ea4gge/A500Mini-Internal-Functional-Keyboard/A500Mini_Photos/3D_Model_New.jpg

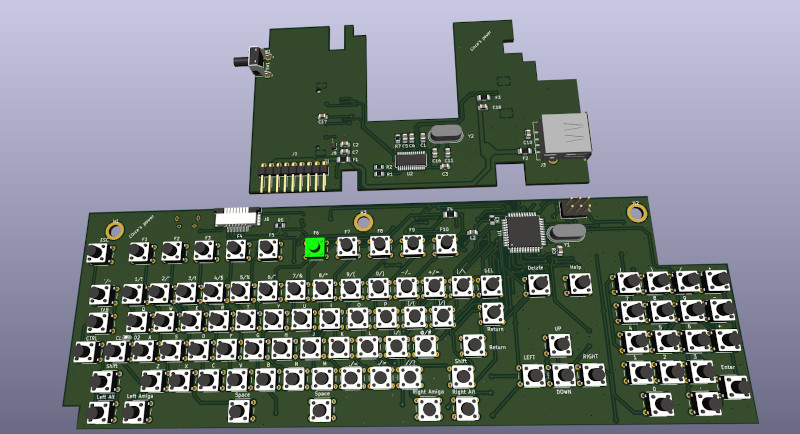
A500Mini_Photos/3D_Model_New.jpg
