ea4gge/A500Mini-Internal-Functional-Keyboard/A500Mini_Photos/0064.jpg

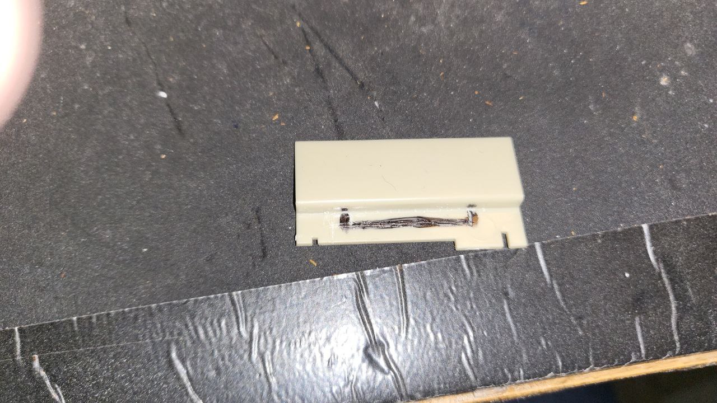
A500Mini_Photos/0064.jpg
