ea4gge/A500Mini-Internal-Functional-Keyboard/A500Mini_Photos/PCB.jpg

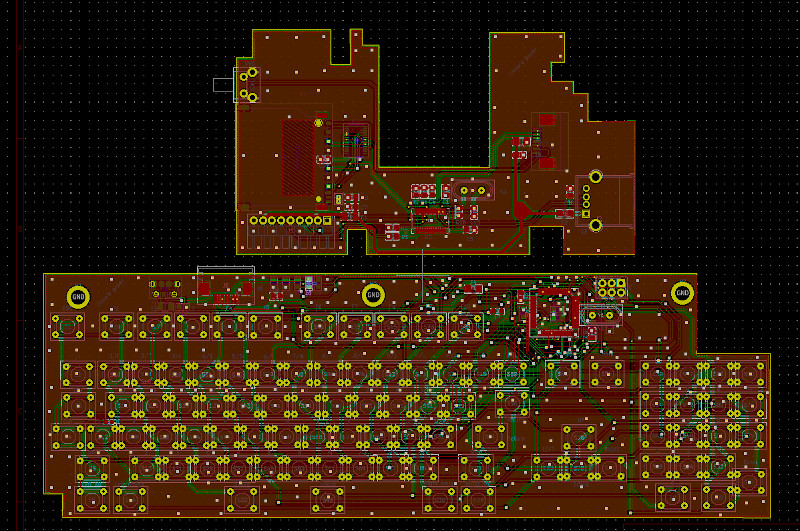
A500Mini_Photos/PCB.jpg
