ea4gge/A500Mini-Internal-Functional-Keyboard/A500Mini_Photos/photo_2022-05-13_19-48-00.jpg

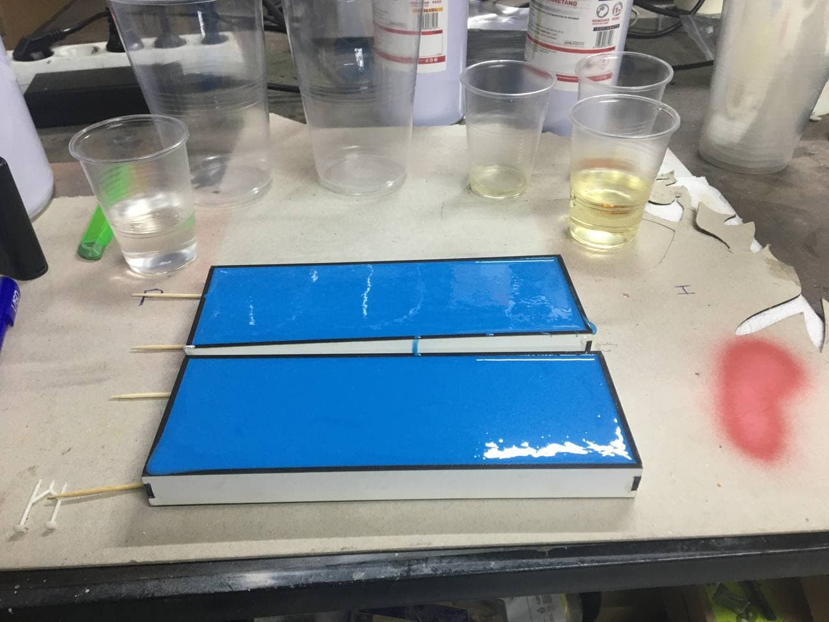
A500Mini_Photos/photo_2022-05-13_19-48-00.jpg
