ea4gge/A500Mini-Internal-Functional-Keyboard/A500Mini_Photos/photo_2022-05-14_19-20-18.jpg

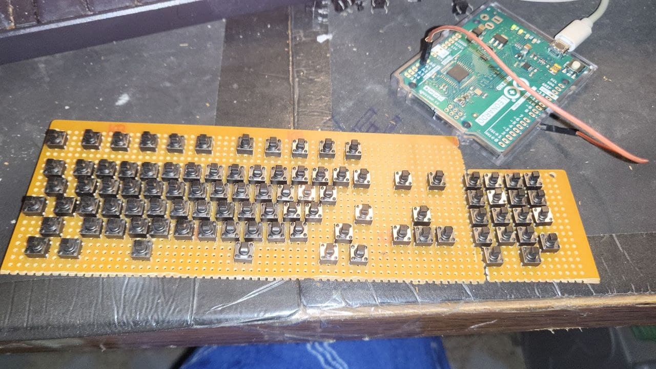
A500Mini_Photos/photo_2022-05-14_19-20-18.jpg
