ea4gge/A500Mini-Internal-Functional-Keyboard/A500Mini_Photos/photo_2022-05-15_17-27-31.jpg

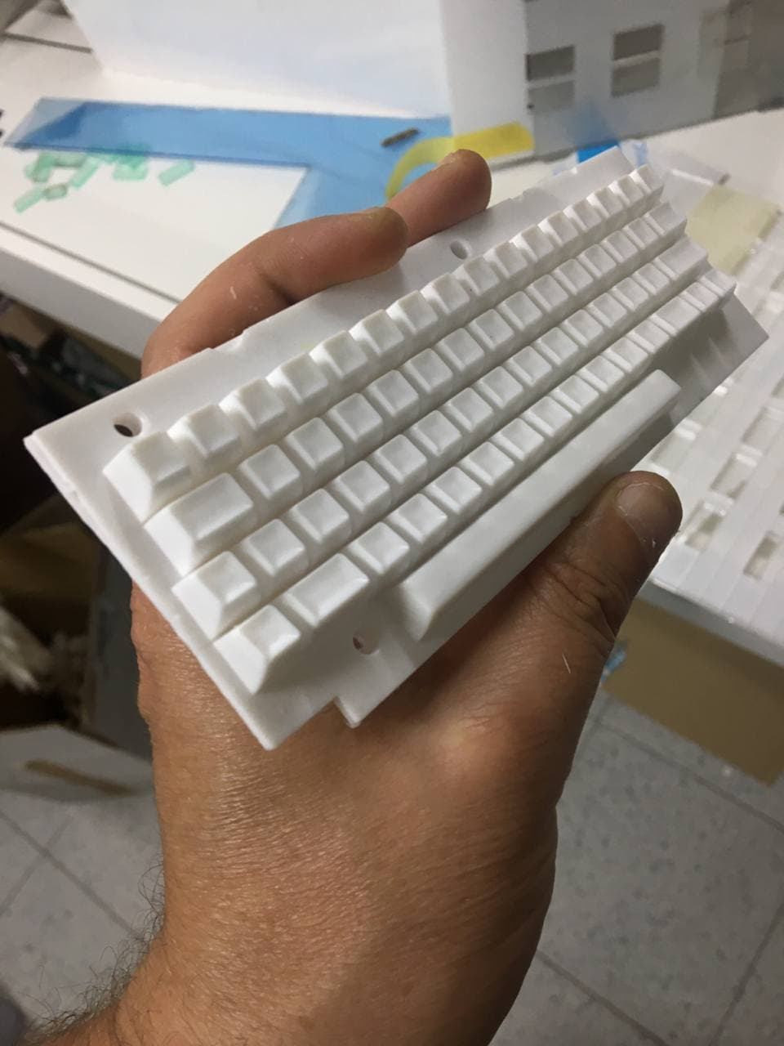
A500Mini_Photos/photo_2022-05-15_17-27-31.jpg
