ea4gge/A500Mini-Internal-Functional-Keyboard/A500Mini_Photos/photo_2022-05-18_14-35-45.jpg

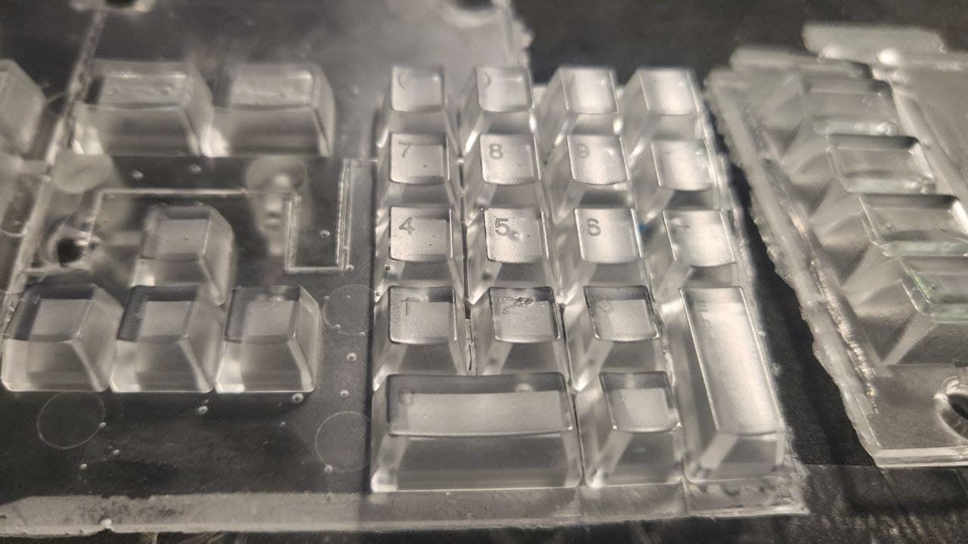
A500Mini_Photos/photo_2022-05-18_14-35-45.jpg
