ea4gge/A500Mini-Internal-Functional-Keyboard/A500Mini_Photos/photo_2022-05-25_00-54-33.jpg

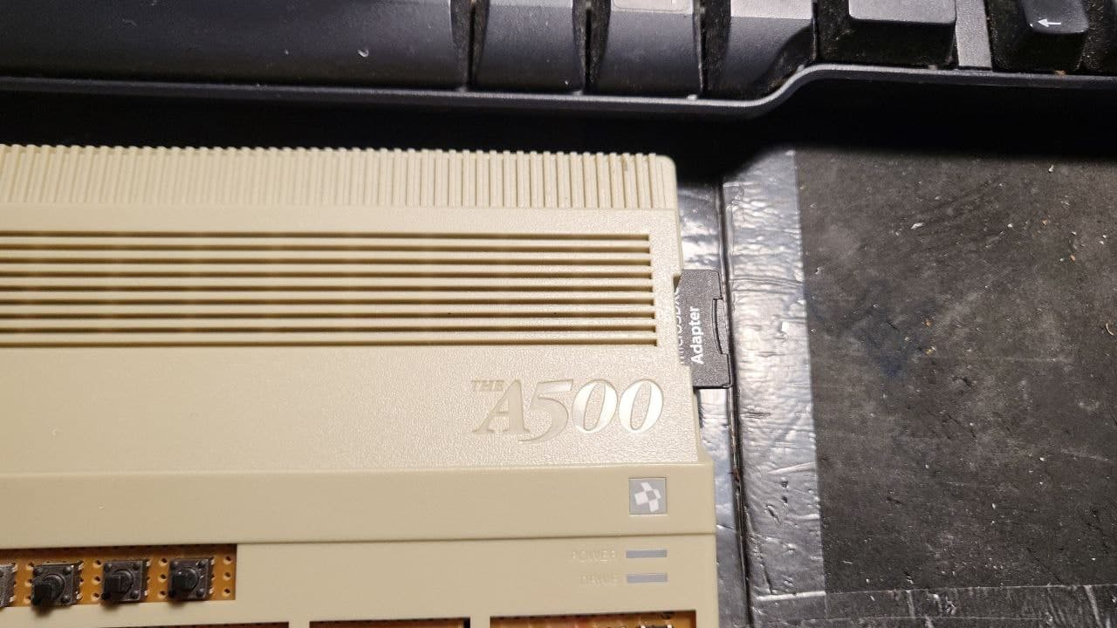
A500Mini_Photos/photo_2022-05-25_00-54-33.jpg
