ea4gge/A500Mini-Internal-Functional-Keyboard/photo_2022-05-14_21-21-15.jpg

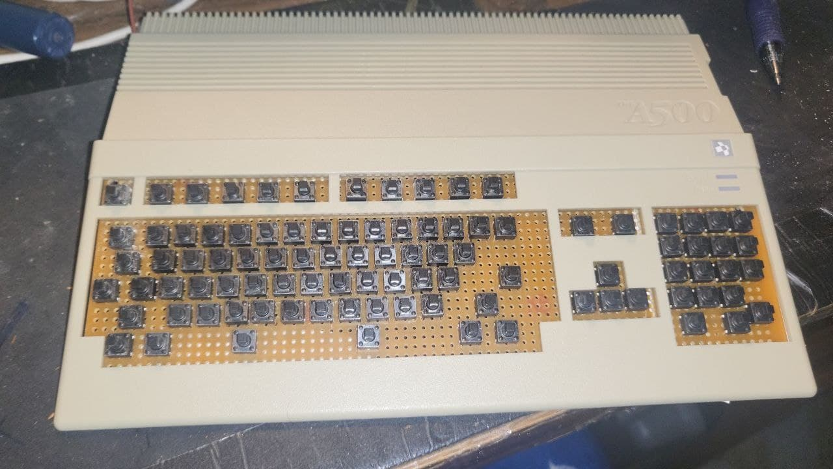
photo_2022-05-14_21-21-15.jpg
